Michael-Beutling/pokeball-autocatcher/Board/Pokeball.sch

## KiCad design Board/Pokeball.sch (2019-08-02)

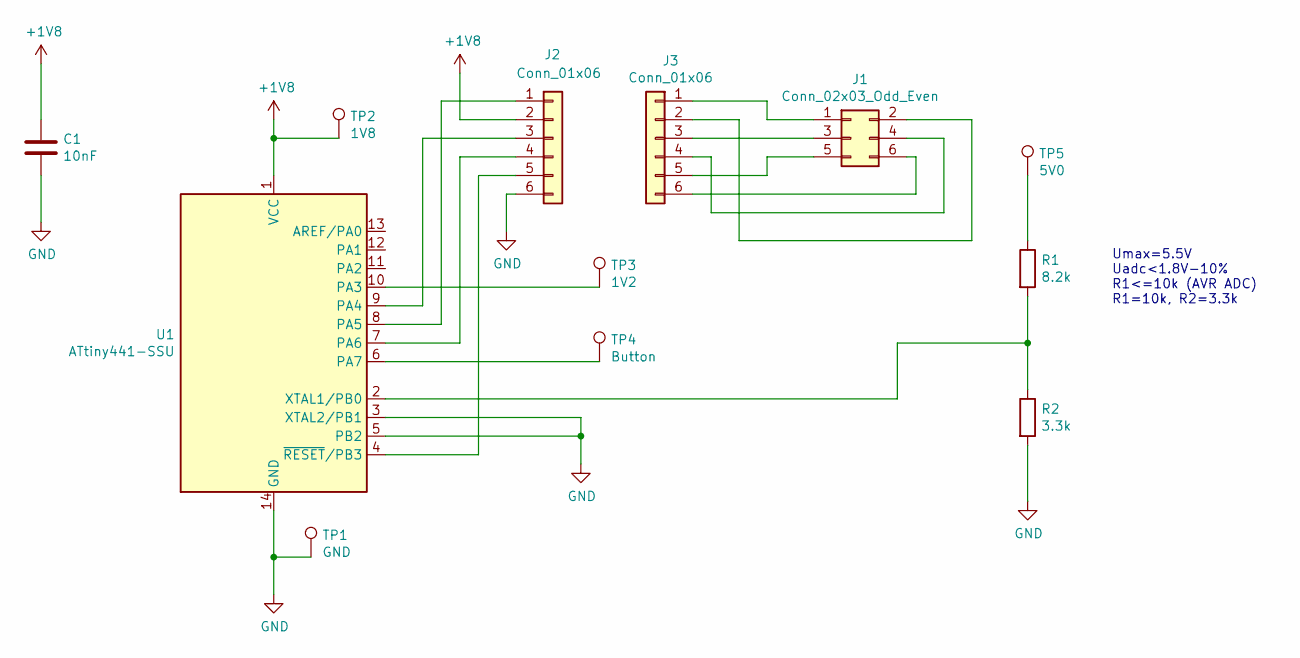
[picture p4: schematic Pokeball.sch]

Parts:
C1: 10nF; C_0603_1608Metric_Pad1.05x0.95mm_HandSolder
J1: Conn_02x03_Odd_Even; PinHeader_2x03_P2.54mm_Vertical
J2: Conn_01x06; ISP_flat_socket
J3: Conn_01x06; ISP_flat_pins
R1: 8.2k; R_0603_1608Metric_Pad1.05x0.95mm_HandSolder
R2: 3.3k; R_0603_1608Metric_Pad1.05x0.95mm_HandSolder
TP1: GND; SingleWire
TP2: 1V8; SingleWire
TP3: 1V2; SingleWire
TP4: Button; SingleWire
TP5: 5V0; SingleWire
U1: ATtiny441-SSU; SOIC-14_3.9x8.7mm_P1.27mm

Connections:
+1V8: C1.1, J2.2, TP2.1, U1.1 (VCC)
GND: C1.2, J2.6, R2.2, TP1.1, U1.3 (XTAL2/PB1), U1.5 (PB2), U1.14 (GND)
unnamed: J1.1, J3.1
unnamed: J1.2, J3.2
unnamed: J1.3, J3.3
unnamed: J1.4, J3.4
unnamed: J1.5, J3.5
unnamed: J1.6, J3.6
unnamed: J2.1, U1.8 (PA5)
unnamed: J2.3, U1.9 (PA4)
unnamed: J2.4, U1.7 (PA6)
unnamed: J2.5, U1.4 (~RESET~/PB3)
unnamed: R1.1, TP5.1
unnamed: R1.2, R2.1, U1.2 (XTAL1/PB0)
unnamed: TP3.1, U1.10 (PA3)
unnamed: TP4.1, U1.6 (PA7)

Notes on the sheet:
Umax=5.5V Uadc<1.8V-10% R1<=10k (AVR ADC) R1=10k, R2=3.3k
